mommel/hs-lr-midi-schwurbler/code/Documentation/SchwurblAir/controller/ButtonController.rst

ButtonController
================

.. toctree::
   :maxdepth: 2

   self

Class ButtonController
----------------------

.. doxygenclass:: ButtonController
   :project: SchwurblAir
   :path: contoller
   :members:
   :protected-members:
   :private-members:
   :undoc-members:
   :outline:
   :no-link:

Typedef MidiTriggerCallbackHandler
----------------------------------

.. doxygentypedef:: MidiTriggerCallbackHandler

ButtonController Implementation
~~~~~~~~~~~~~~~~~~~~~~~~~~~~~~~

.. doxygenfile:: controller/button_controller.cpp
