mommel/hs-lr-midi-schwurbler/code/Documentation/SchwurblAir/controller/index.rst

.. _schwurbler360_controller:

Controller
==========

.. toctree::
    :maxdepth: 1

    ButtonController
    PotiController
