mommel/hs-lr-midi-schwurbler/code/Documentation/Schwurbler360/controller/index.rst

.. _schwurbler360_controller:

Controller
==========

.. toctree::
    :maxdepth: 1

    ButtonController
    RotaryController
