mommel/hs-lr-midi-schwurbler/assets/Helpneeded.bmp

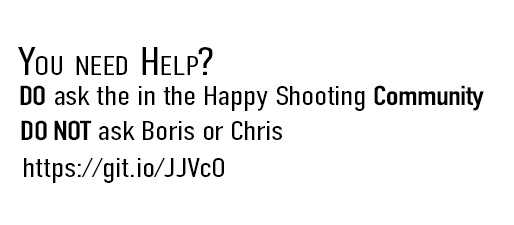
assets/Helpneeded.bmp
