mommel/hs-lr-midi-schwurbler/assets/MidiDevice.png

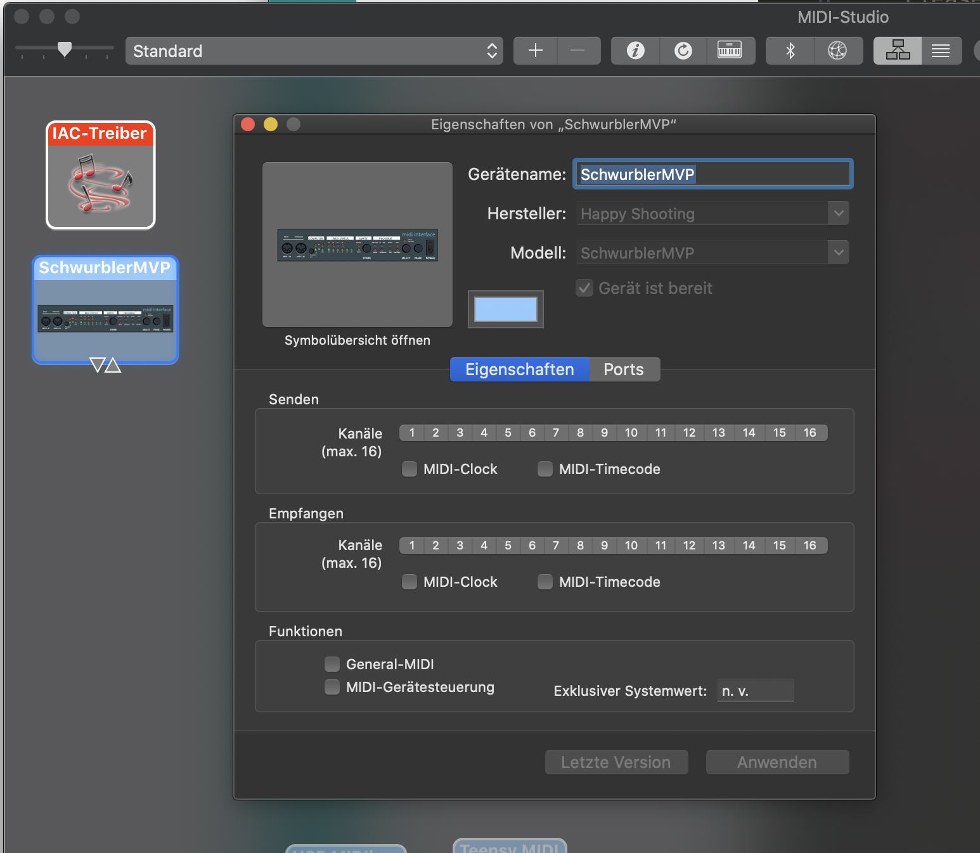
assets/MidiDevice.png
