mommel/hs-lr-midi-schwurbler/assets/UsbDevice.png

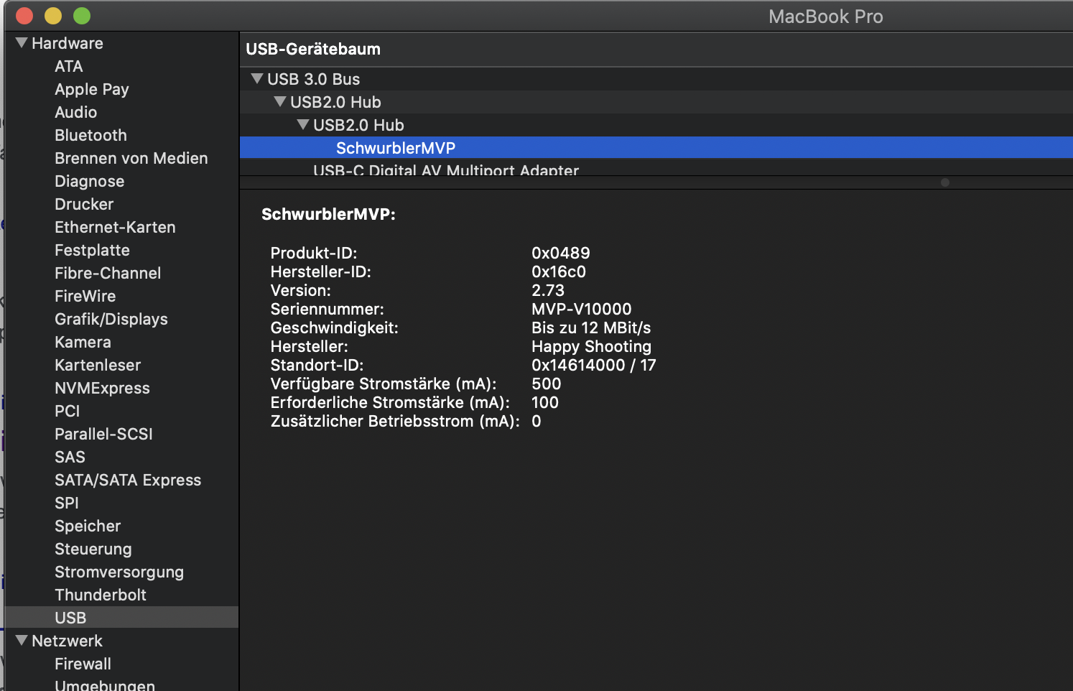
assets/UsbDevice.png
