mommel/hs-lr-midi-schwurbler/assets/windows-usb.jpg

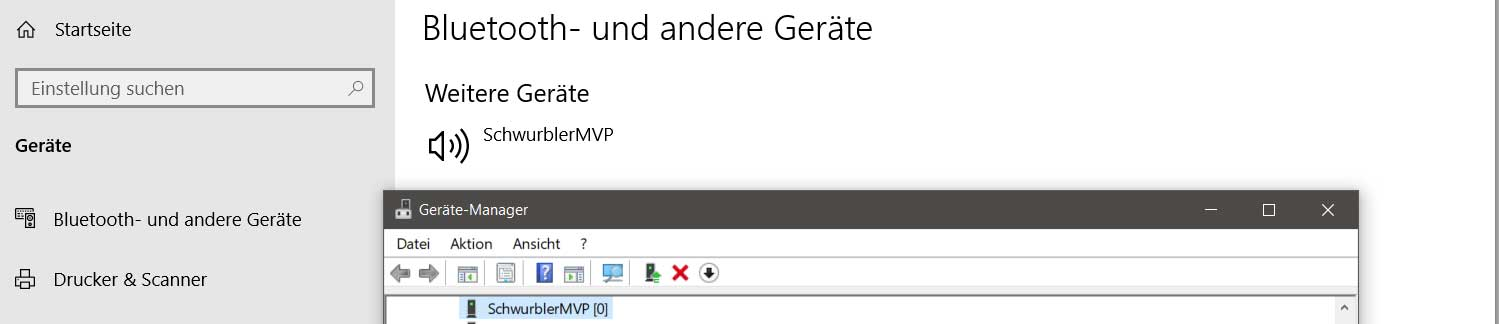
assets/windows-usb.jpg
