mommel/hs-lr-midi-schwurbler/assets/windows_midi.jpg

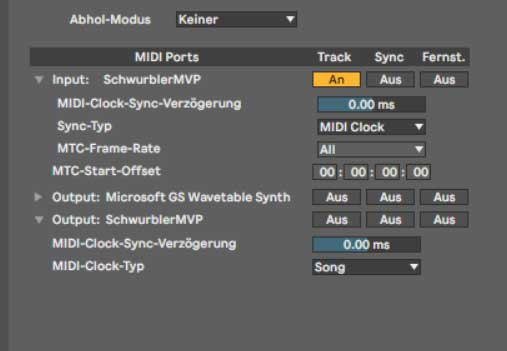
assets/windows_midi.jpg
