mommel/hs-lr-midi-schwurbler/circuit-diagram/MVP/schema-shorts.jpg

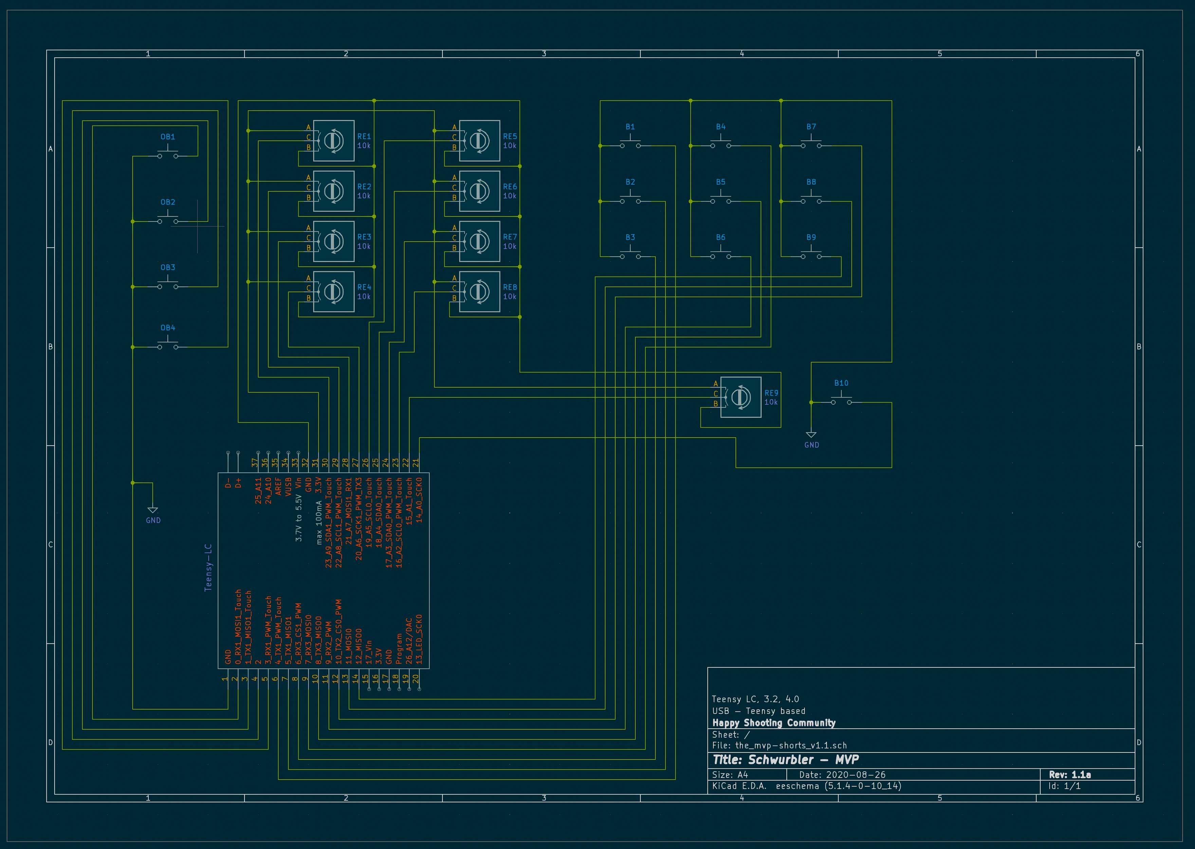
circuit-diagram/MVP/schema-shorts.jpg
