mommel/hs-lr-midi-schwurbler/circuit-diagram/MVP/schema.jpg

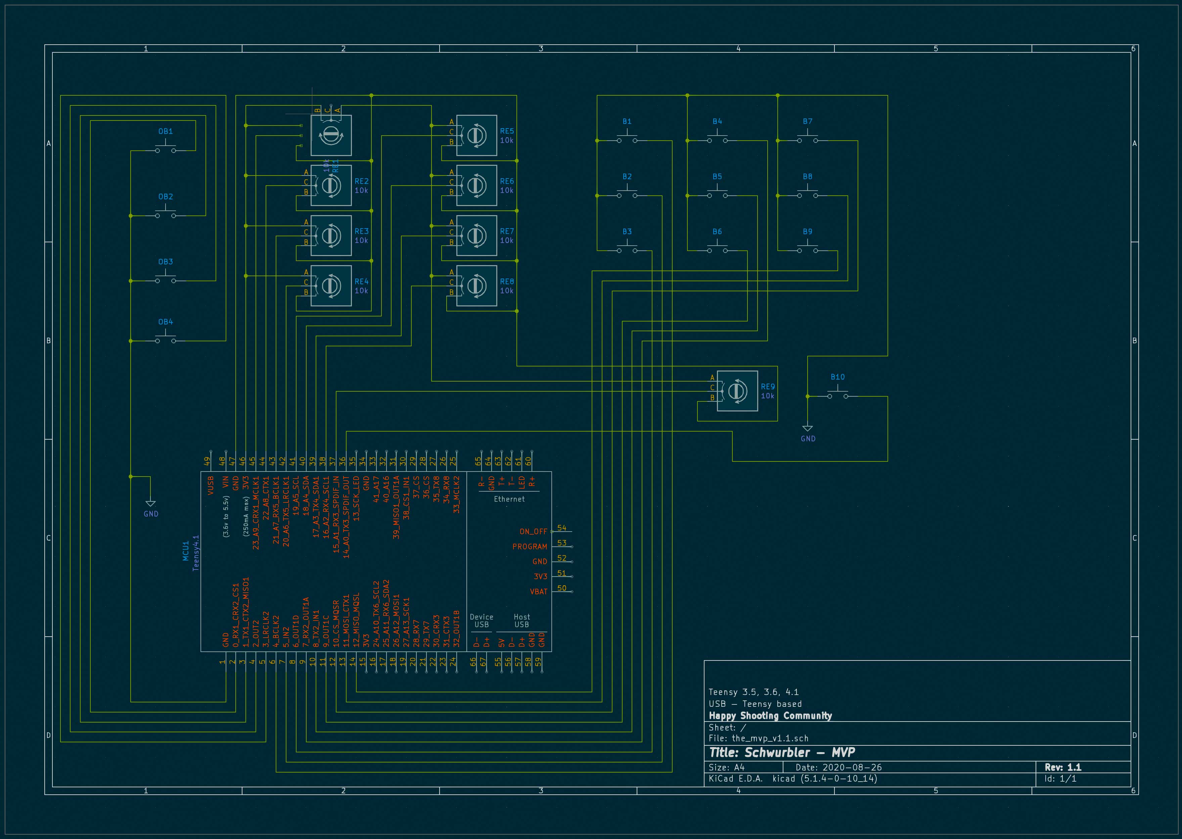
circuit-diagram/MVP/schema.jpg
