mommel/hs-lr-midi-schwurbler/design-drafts/Interface-Schwurbler-F1.png

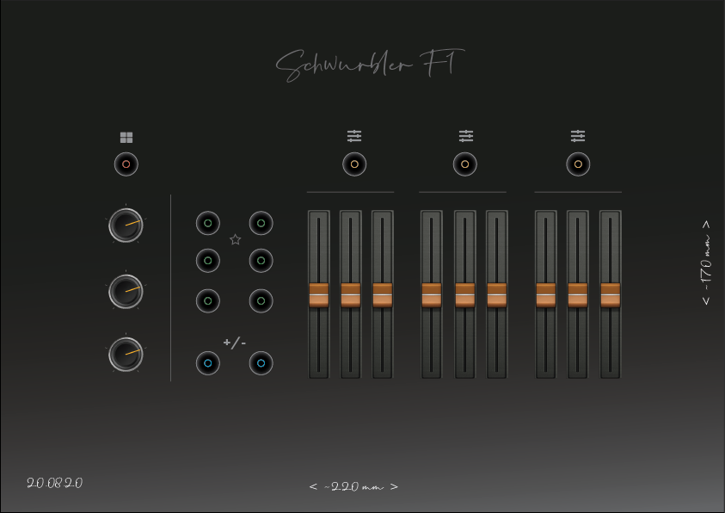
design-drafts/Interface-Schwurbler-F1.png
