mommel/hs-lr-midi-schwurbler/design-drafts/Interface-Schwurbler-R1.png

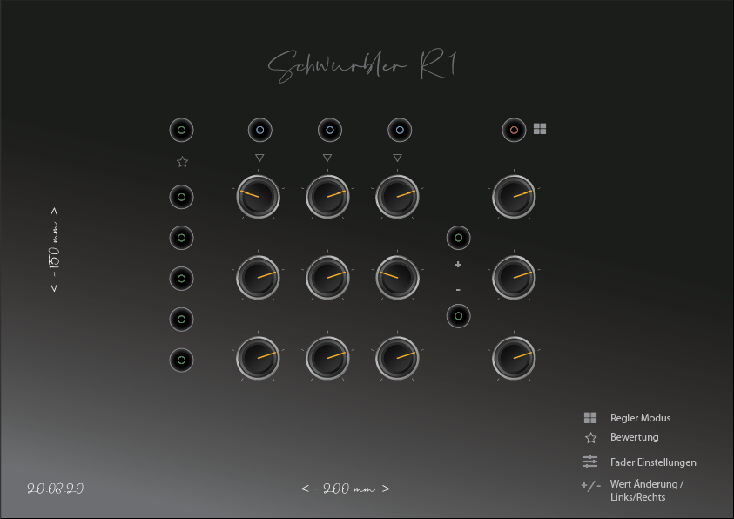
design-drafts/Interface-Schwurbler-R1.png
