mommel/hs-lr-midi-schwurbler/design-drafts/SchwurblerV1.png

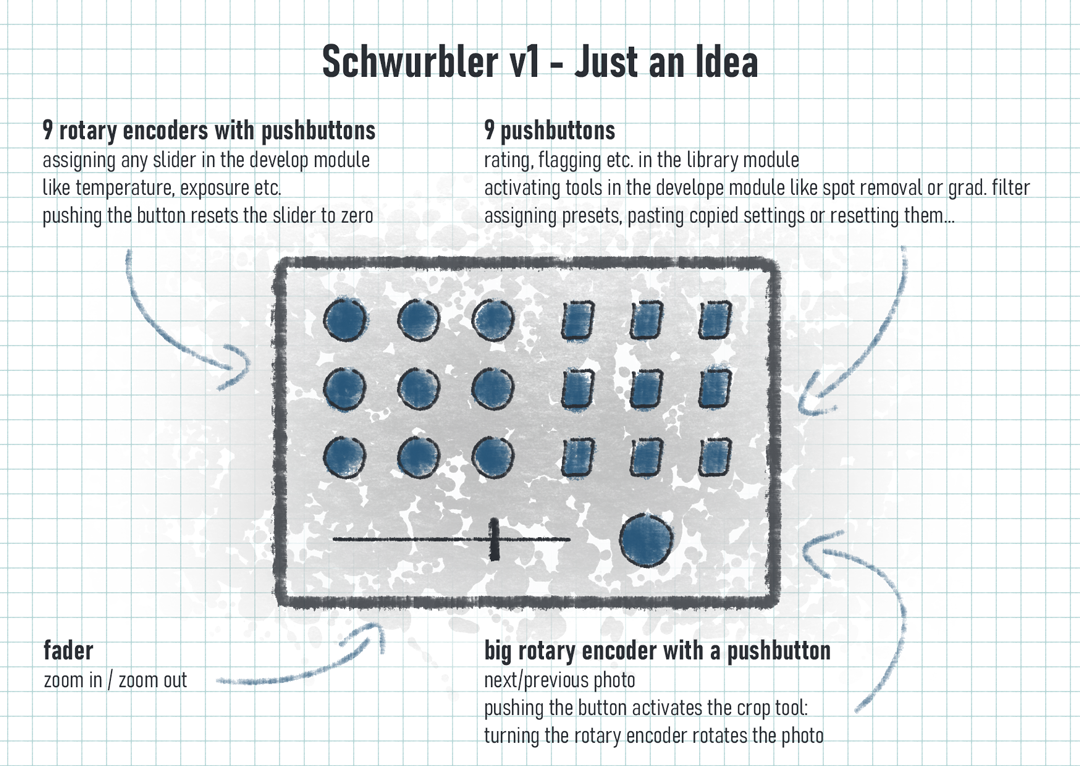
design-drafts/SchwurblerV1.png
