mommel/hs-lr-midi-schwurbler/images-wiki/Der-Schwurbler-MVP-Platine.jpg

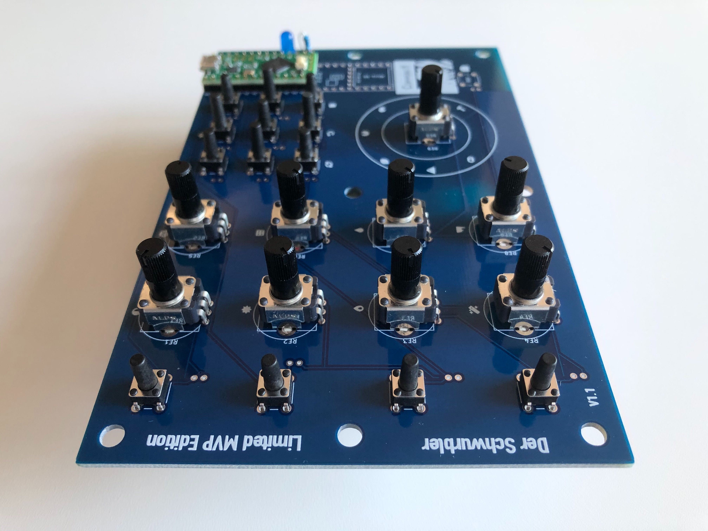
images-wiki/Der-Schwurbler-MVP-Platine.jpg
