mommel/hs-lr-midi-schwurbler/images-wiki/MVP-schwurbler_ii_v2.jpg

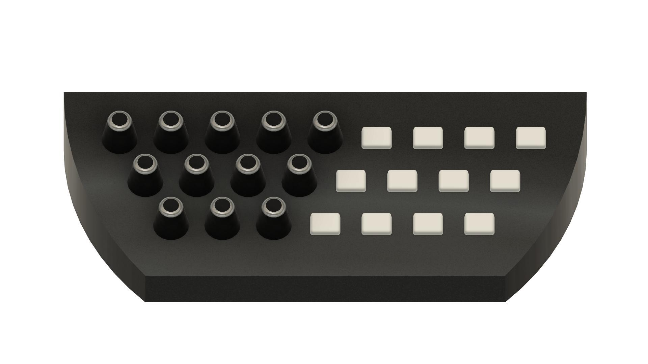
images-wiki/MVP-schwurbler_ii_v2.jpg
