mommel/hs-lr-midi-schwurbler/images-wiki/MVP-schwurbler_v1.png

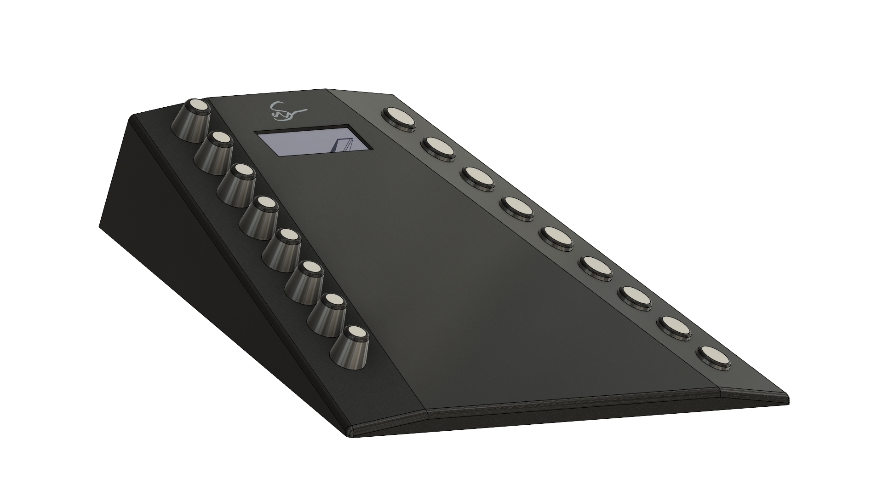
images-wiki/MVP-schwurbler_v1.png
