mommel/hs-lr-midi-schwurbler/images-wiki/mvp-version_designx2_v2.png

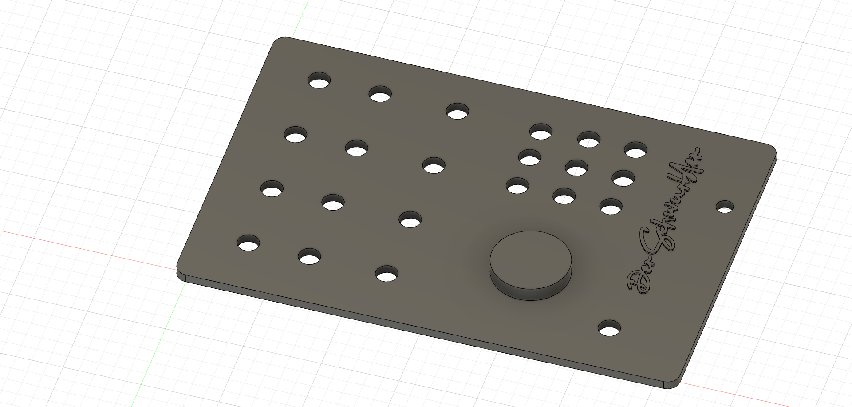
images-wiki/mvp-version_designx2_v2.png
