mommel/hs-lr-midi-schwurbler/images-wiki/Teensy-LC-and-4-1.jpg

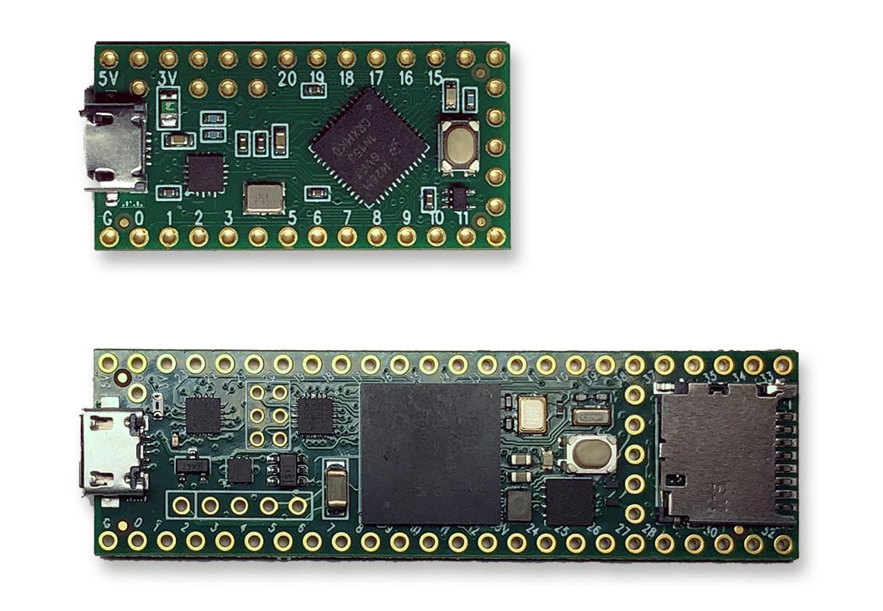
images-wiki/Teensy-LC-and-4-1.jpg
