mommel/hs-lr-midi-schwurbler/pcb/MVP/Render/back_mounted_pre.jpg

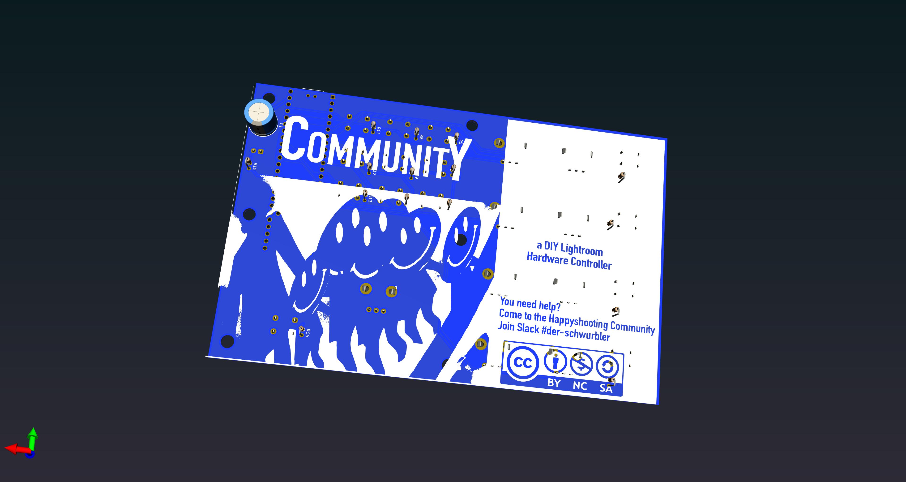
pcb/MVP/Render/back_mounted_pre.jpg
