mommel/hs-lr-midi-schwurbler/pcb/MVP/Render/back_mounted_ray.jpg

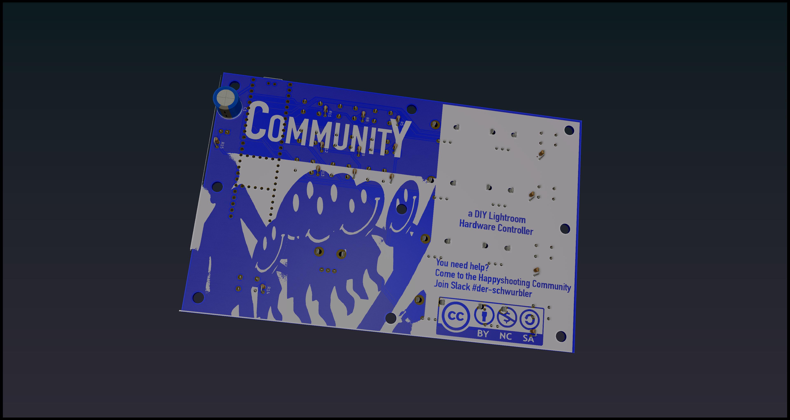
pcb/MVP/Render/back_mounted_ray.jpg
