mommel/hs-lr-midi-schwurbler/pcb/MVP/Render/back_unmounted_ray.jpg

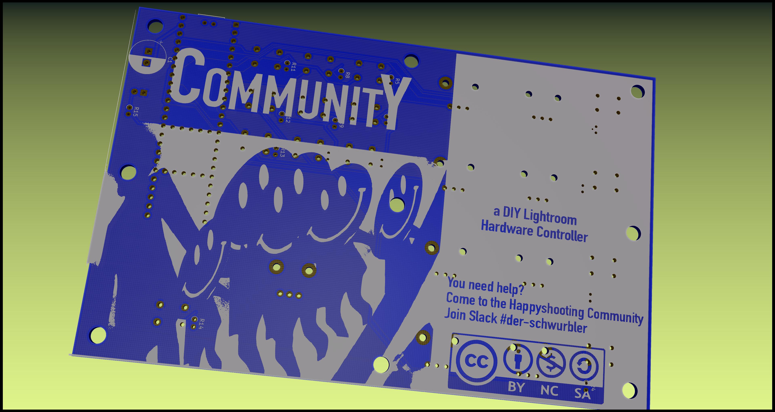
pcb/MVP/Render/back_unmounted_ray.jpg
