mommel/hs-lr-midi-schwurbler/pcb/MVP/Render/front_unmounted_ray.jpg

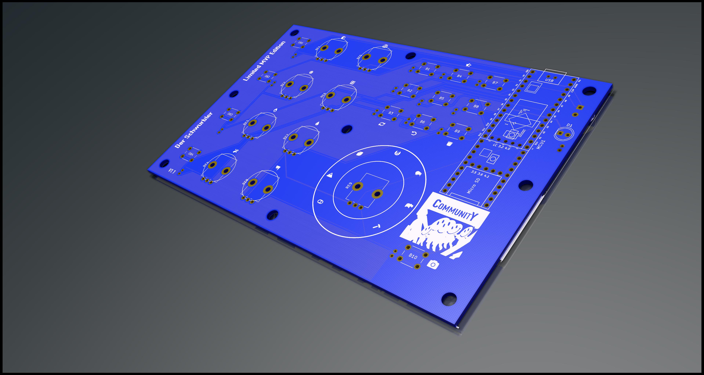
pcb/MVP/Render/front_unmounted_ray.jpg
