mommel/hs-lr-midi-schwurbler/pcb/MVP/Render/MVP Render_1231.png

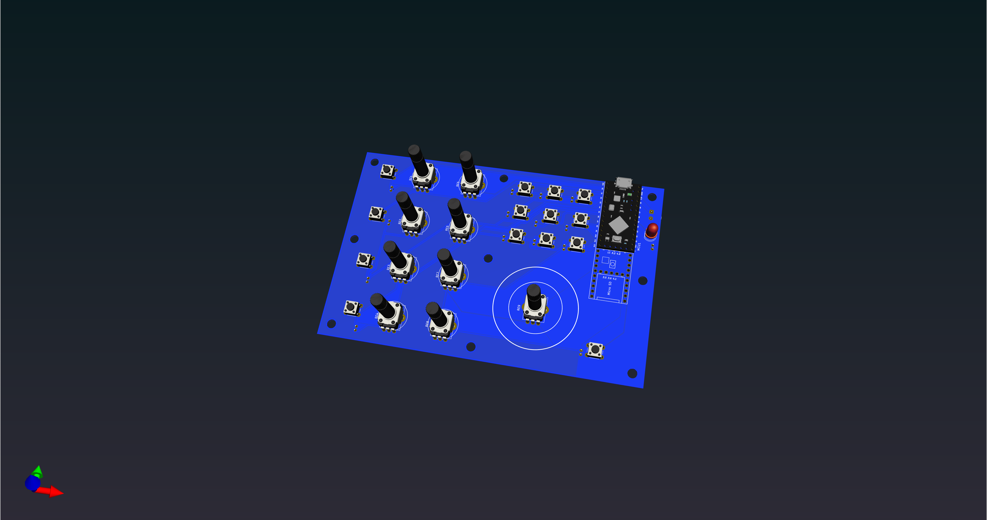
pcb/MVP/Render/MVP Render_1231.png
