mommel/hs-lr-midi-schwurbler/pcb/MVP/Render/MVP Render_1232.png

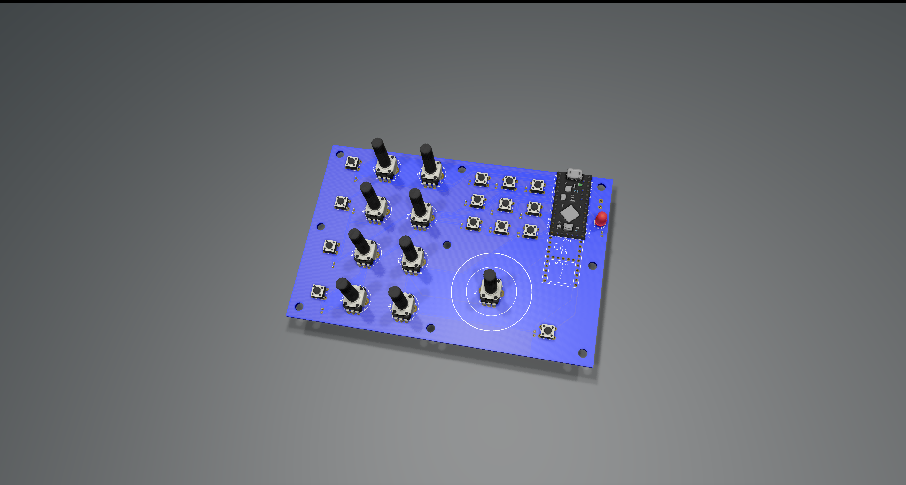
pcb/MVP/Render/MVP Render_1232.png
