mommel/hs-lr-midi-schwurbler/pcb/MVP/Render/the_mvp_v1.2.jpg

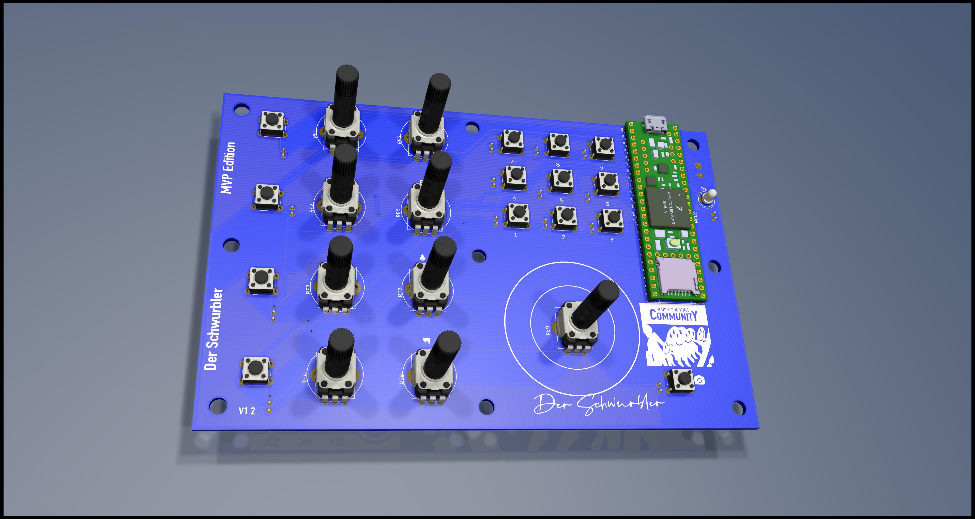
pcb/MVP/Render/the_mvp_v1.2.jpg
