mommel/hs-lr-midi-schwurbler/prototyping/MVP/themvp_Steckplatine.jpg

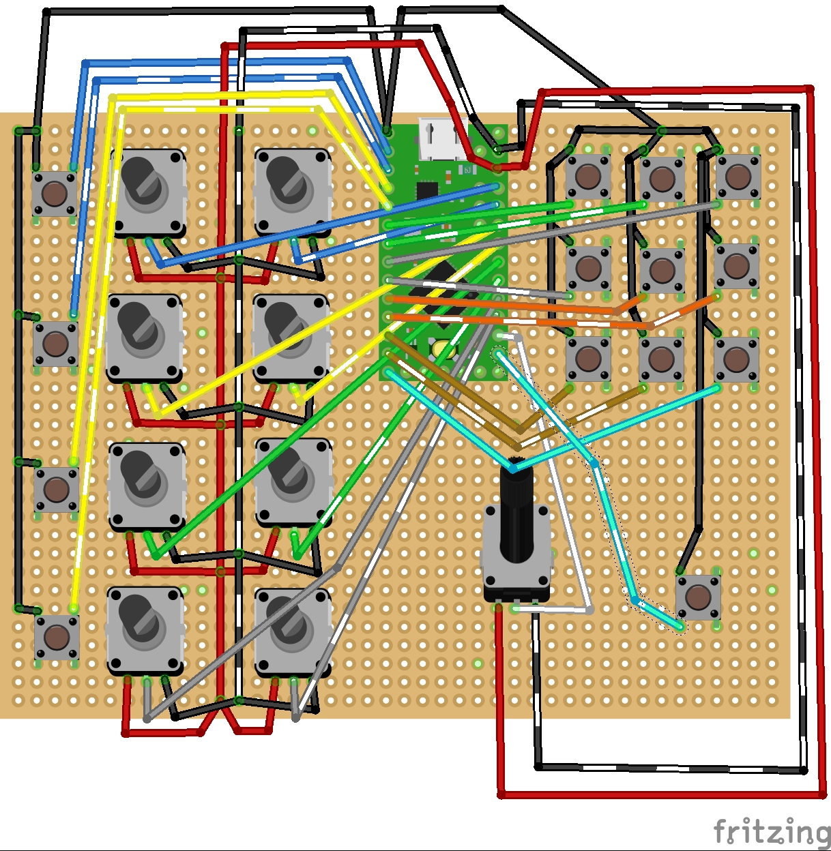
prototyping/MVP/themvp_Steckplatine.jpg
