mommel/hs-lr-midi-schwurbler/images-wiki/Der-Schwurbler-MVP-Parts.jpg

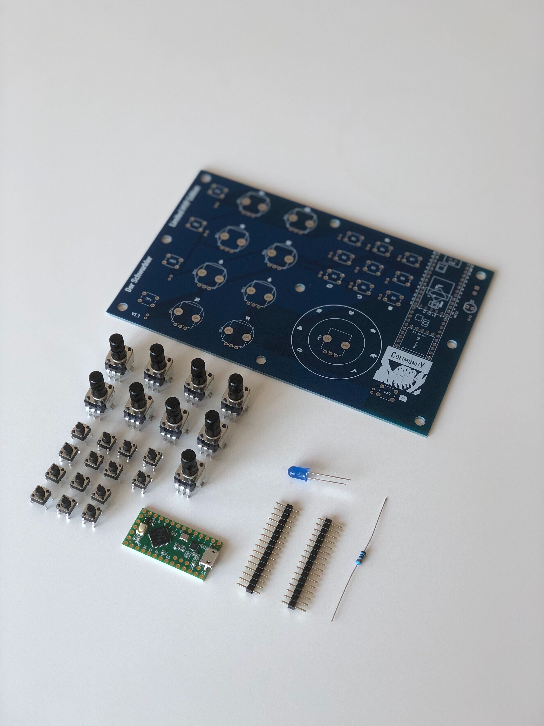
images-wiki/Der-Schwurbler-MVP-Parts.jpg
