mommel/hs-lr-midi-schwurbler/3d-prints/MVP/3D-printed case.png

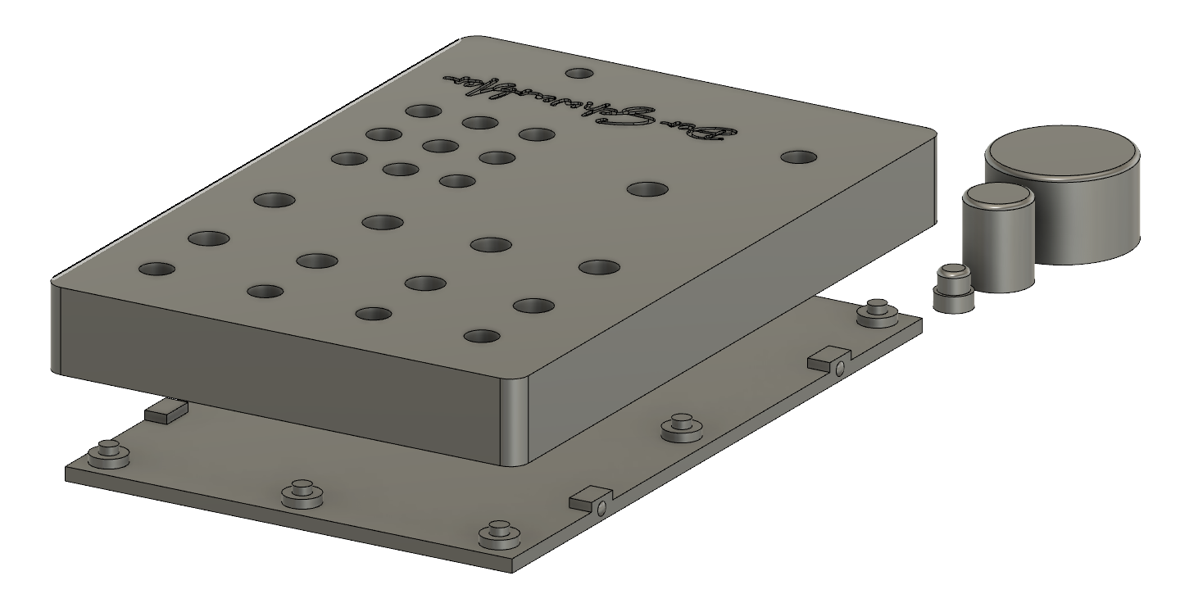
3d-prints/MVP/3D-printed case.png
