mommel/hs-lr-midi-schwurbler/quickstartguide/MVP/de/Der Schwurbler MVP - Schnellstart_Seite_6.jpg

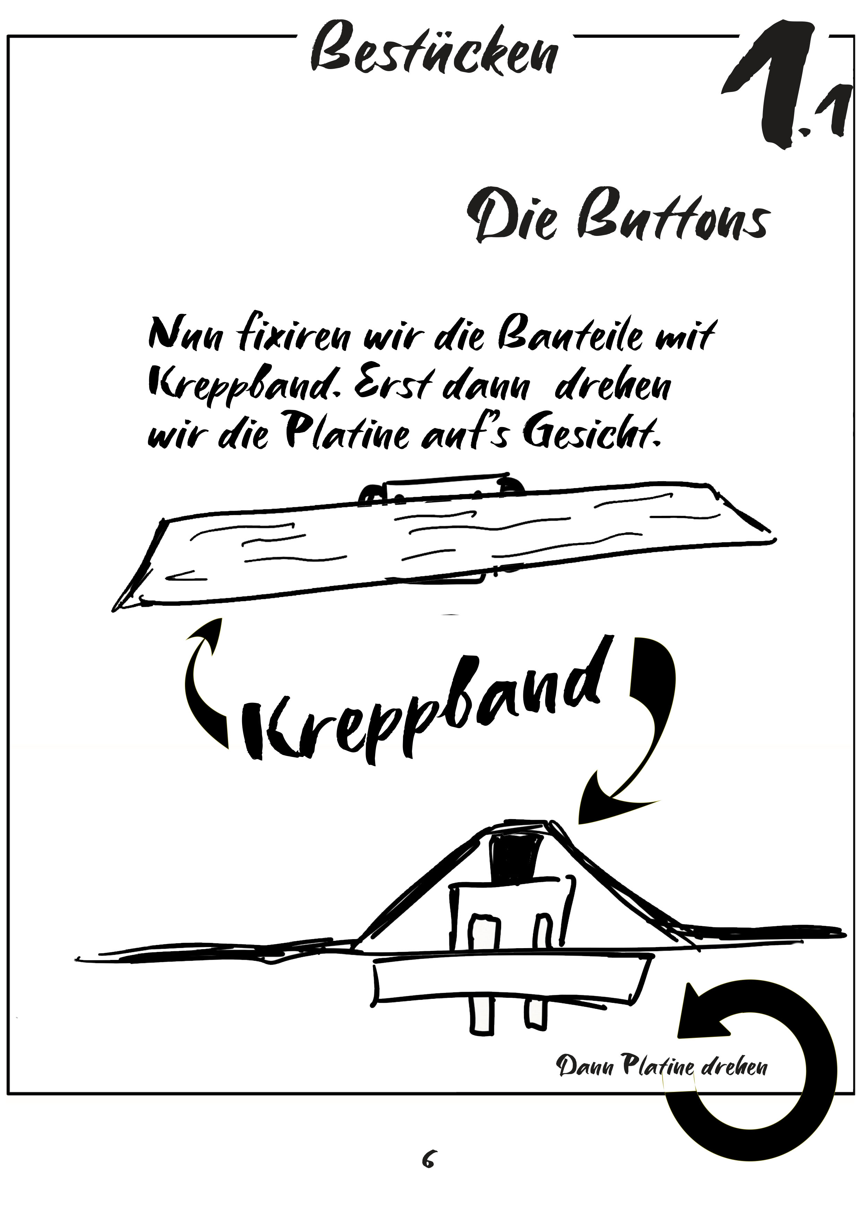
quickstartguide/MVP/de/Der Schwurbler MVP - Schnellstart_Seite_6.jpg
